Unkn0wn-cs/Outcasts/schemes/Scheme.png

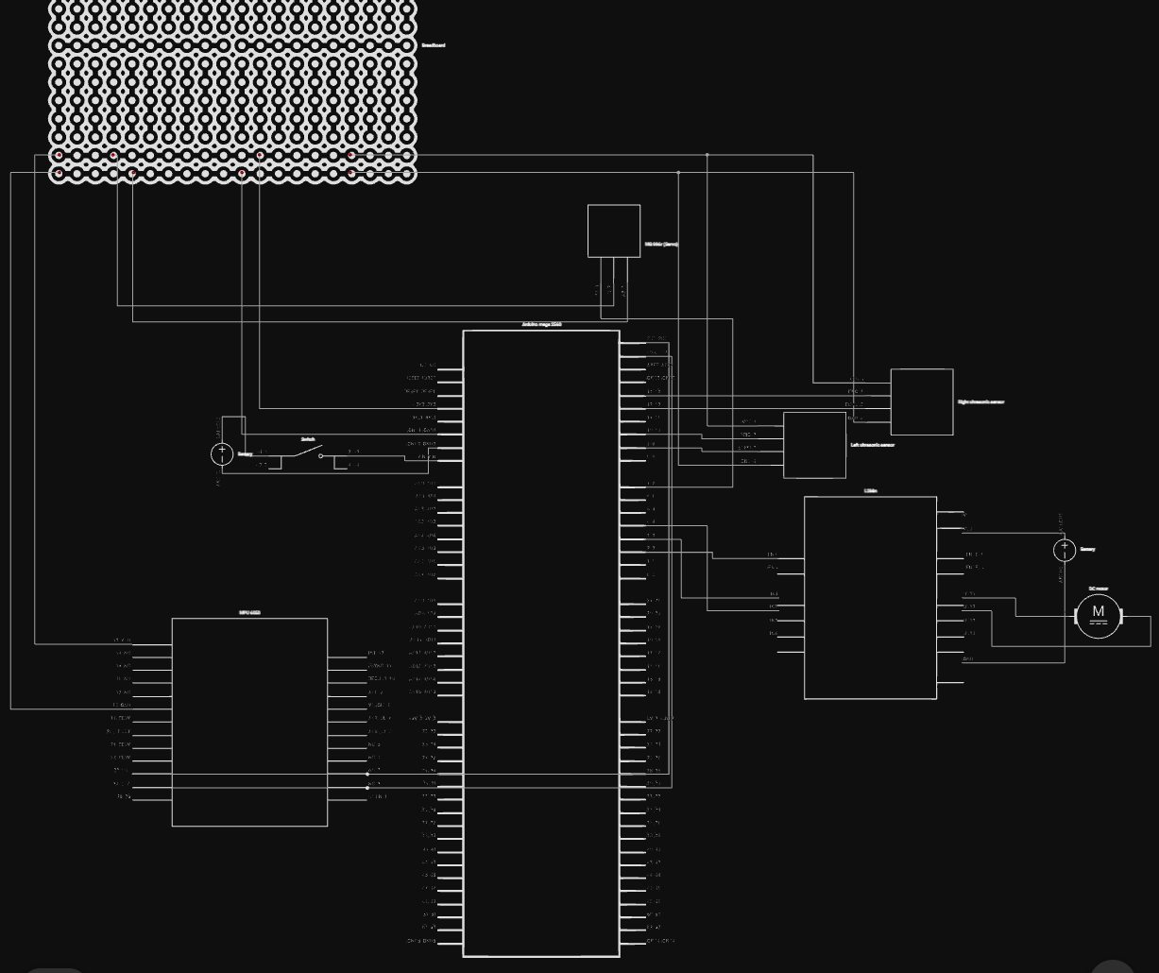
schemes/Scheme.png
