Unkn0wn-cs/Outcasts/t-photos/Serious Men.jpg

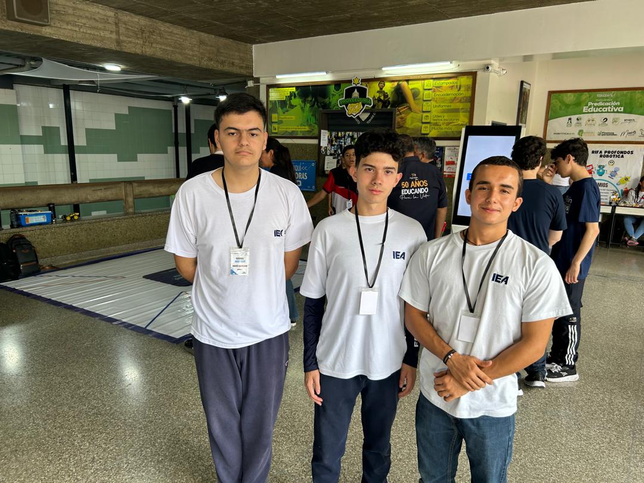
t-photos/Serious Men.jpg
