Unkn0wn-cs/Outcasts/v-photos/back.jpg

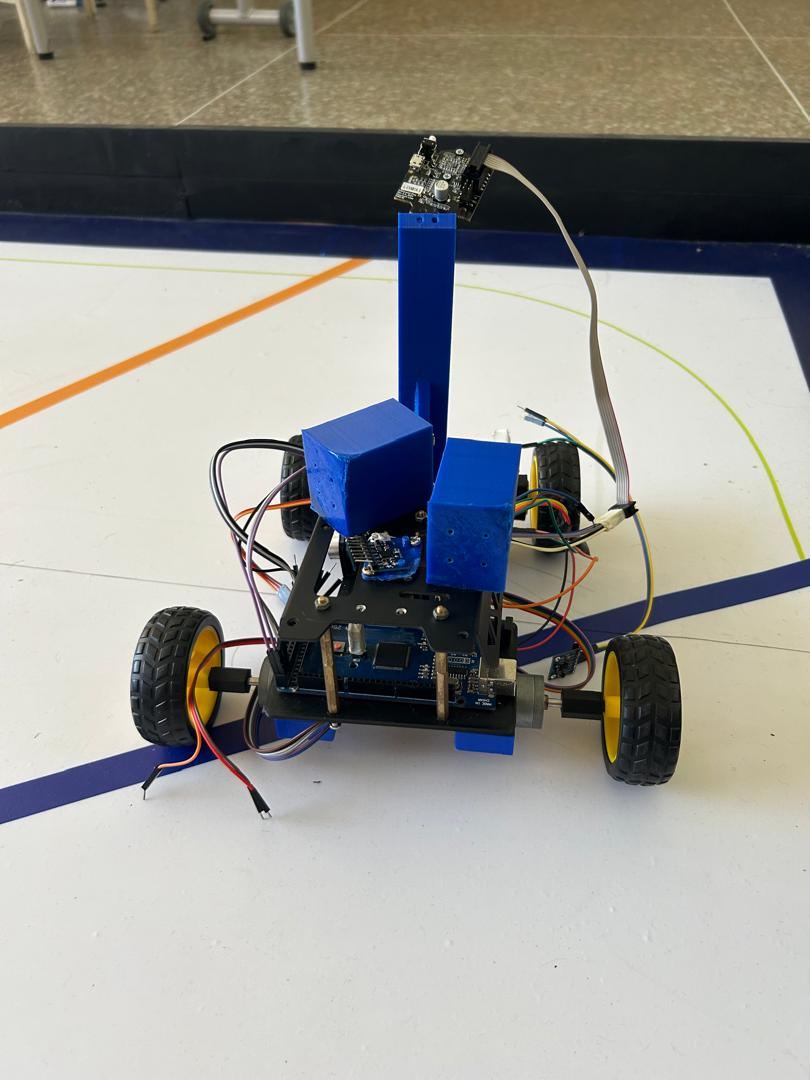
v-photos/back.jpg
