Unkn0wn-cs/Outcasts/v-photos/bottom.jpg

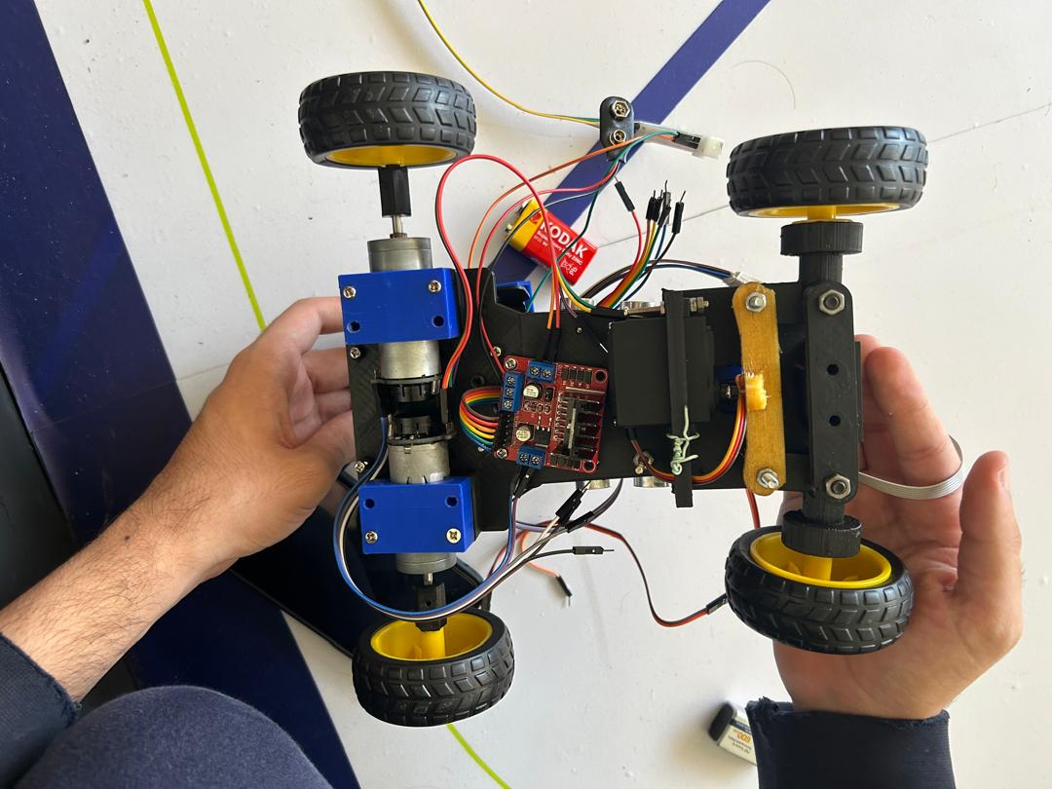
v-photos/bottom.jpg
