Unkn0wn-cs/Outcasts/v-photos/front.jpg

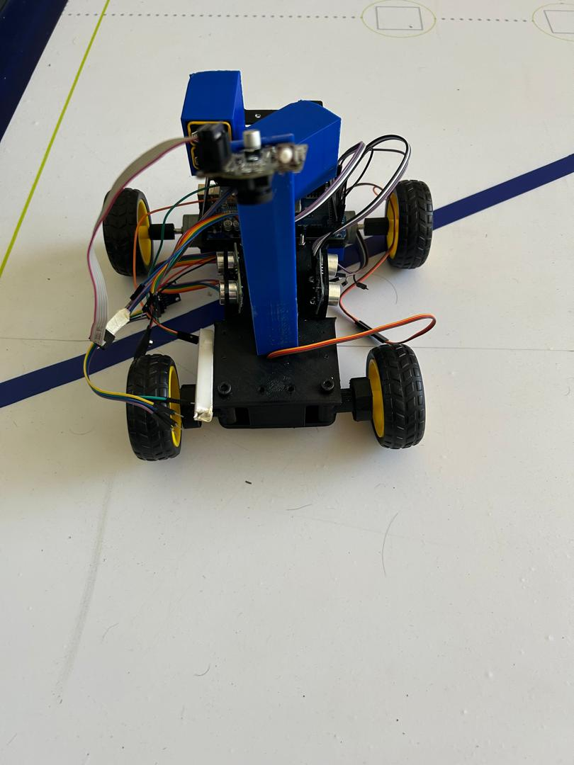
v-photos/front.jpg
