Unkn0wn-cs/Outcasts/v-photos/left.jpg

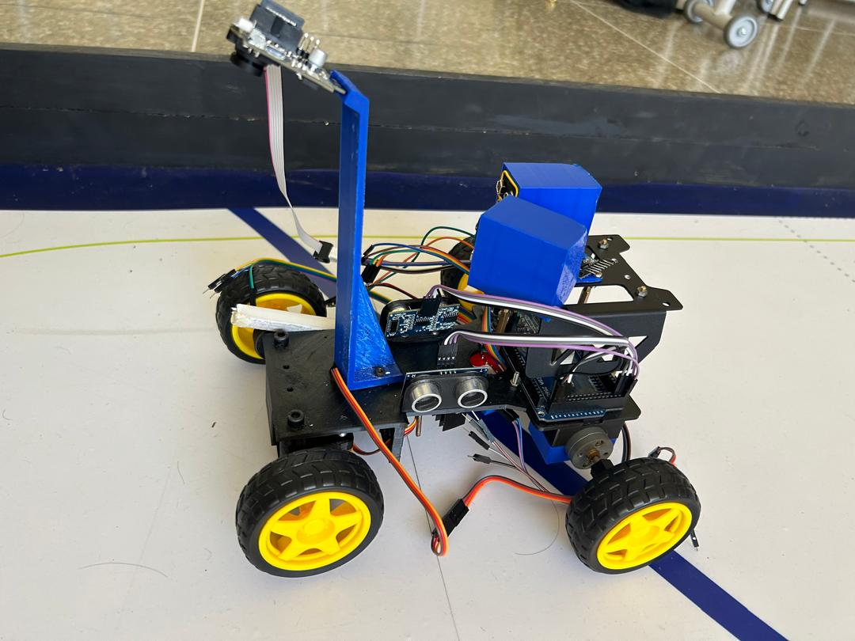
v-photos/left.jpg
