Unkn0wn-cs/Outcasts/v-photos/right.jpg

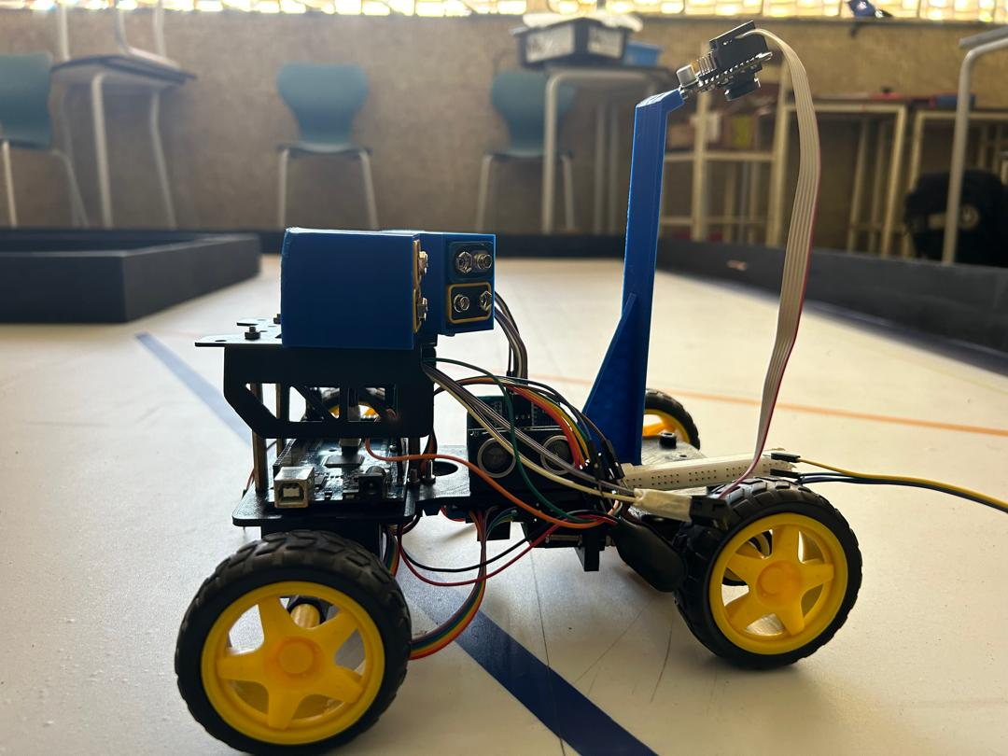
v-photos/right.jpg
