Unkn0wn-cs/Outcasts/v-photos/top.jpg

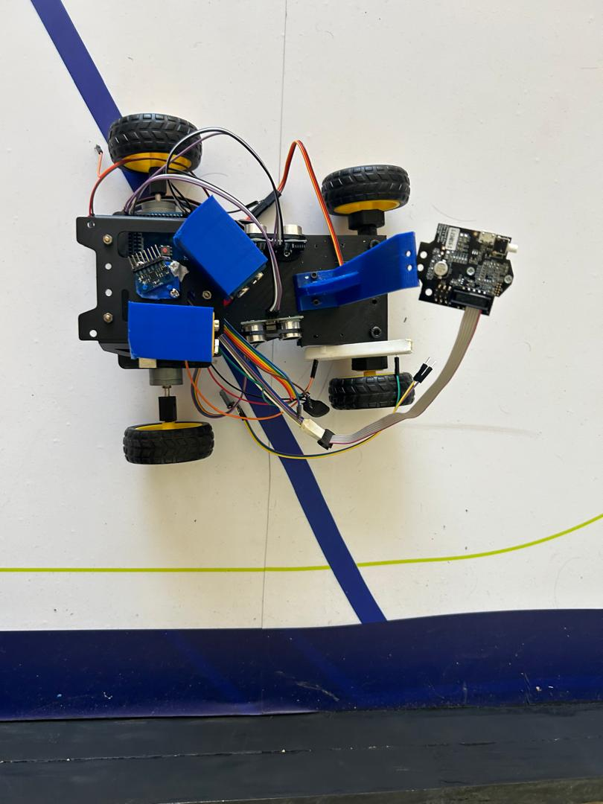
v-photos/top.jpg
