Unkn0wn-cs/Outcasts/src/Movement/90grd/90grd.ino

/* Sweep
 by BARRAGAN <http://barraganstudio.com>
 This example code is in the public domain.

 modified 8 Nov 2013
 by Scott Fitzgerald
 https://www.arduino.cc/en/Tutorial/LibraryExamples/Sweep
*/

#include <Servo.h>

Servo myservo;  // create servo object to control a servo
// twelve servo objects can be created on most boards

int pos = 0;    // variable to store the servo position

void setup() {
  myservo.attach(7);  // attaches the servo on pin 9 to the servo object
}

void loop() { 
myservo.write(145);                  // waits 15 ms for the servo to reach the position
  
}
